svenpetersen1965/PET-SNES-Gamepad-Adapter/Case/Rev. 0/Label/Label.png

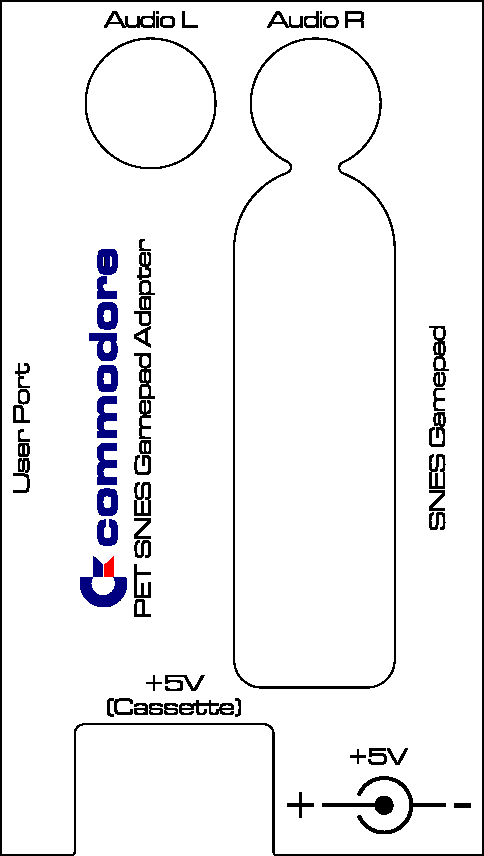
Case/Rev. 0/Label/Label.png
