svenpetersen1965/PET-SNES-Gamepad-Adapter/Rev. 1/pictures/4251_-_SNES_Gamepad_Adapter_C64.JPG

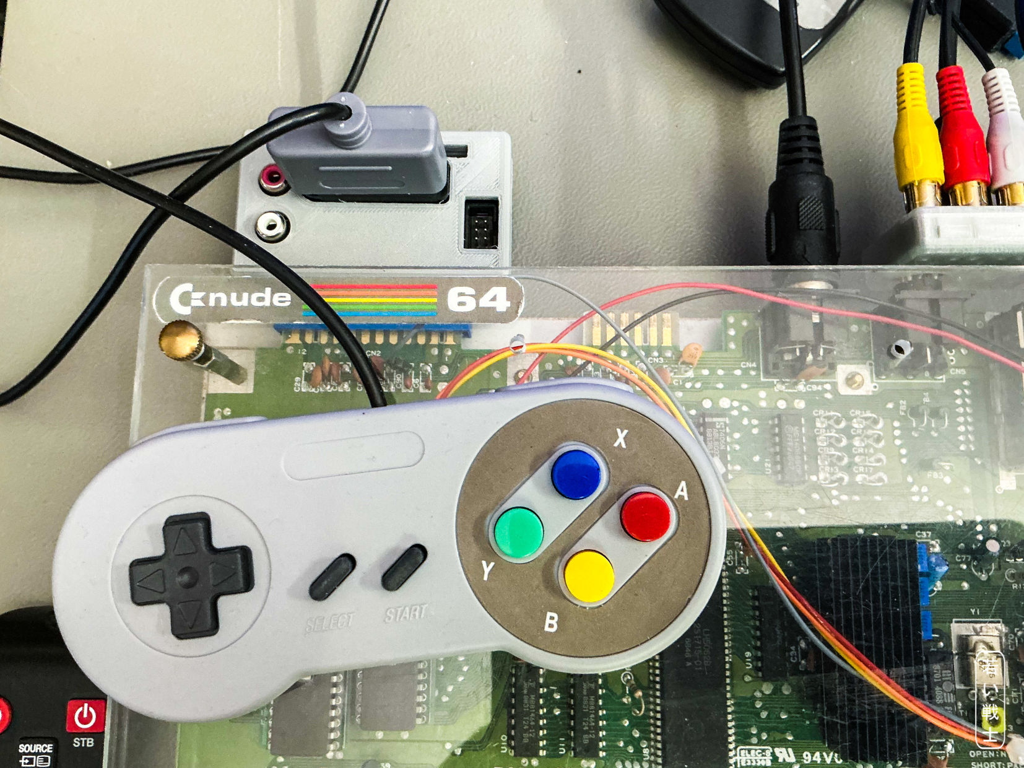
Rev. 1/pictures/4251_-_SNES_Gamepad_Adapter_C64.JPG
